OmniLoco/OmniLoco-Hardware/OmniRotor/Artwork/servo-pin-2.bmp

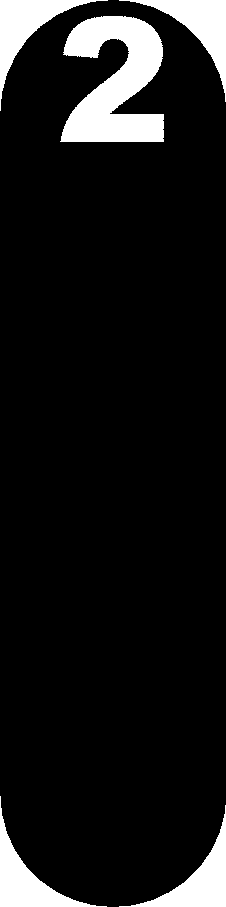
OmniRotor/Artwork/servo-pin-2.bmp
