OmniLoco/OmniLoco-Hardware/OmniRotor/Artwork/servo-pin-4.bmp

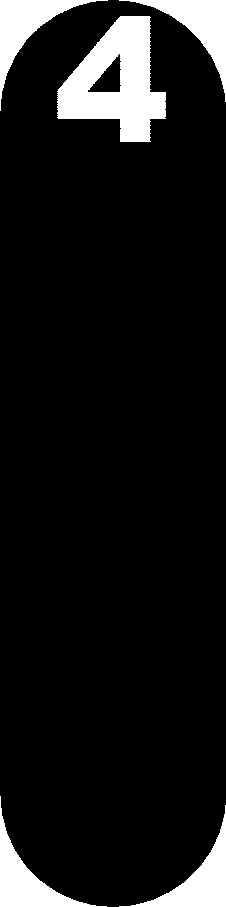
OmniRotor/Artwork/servo-pin-4.bmp
